Panko74/ESP32-Remote-CW-Keyer/schema/ESP32Keyer.kicad_sch

## KiCad design schema/ESP32Keyer.kicad_sch (2026-07-10)

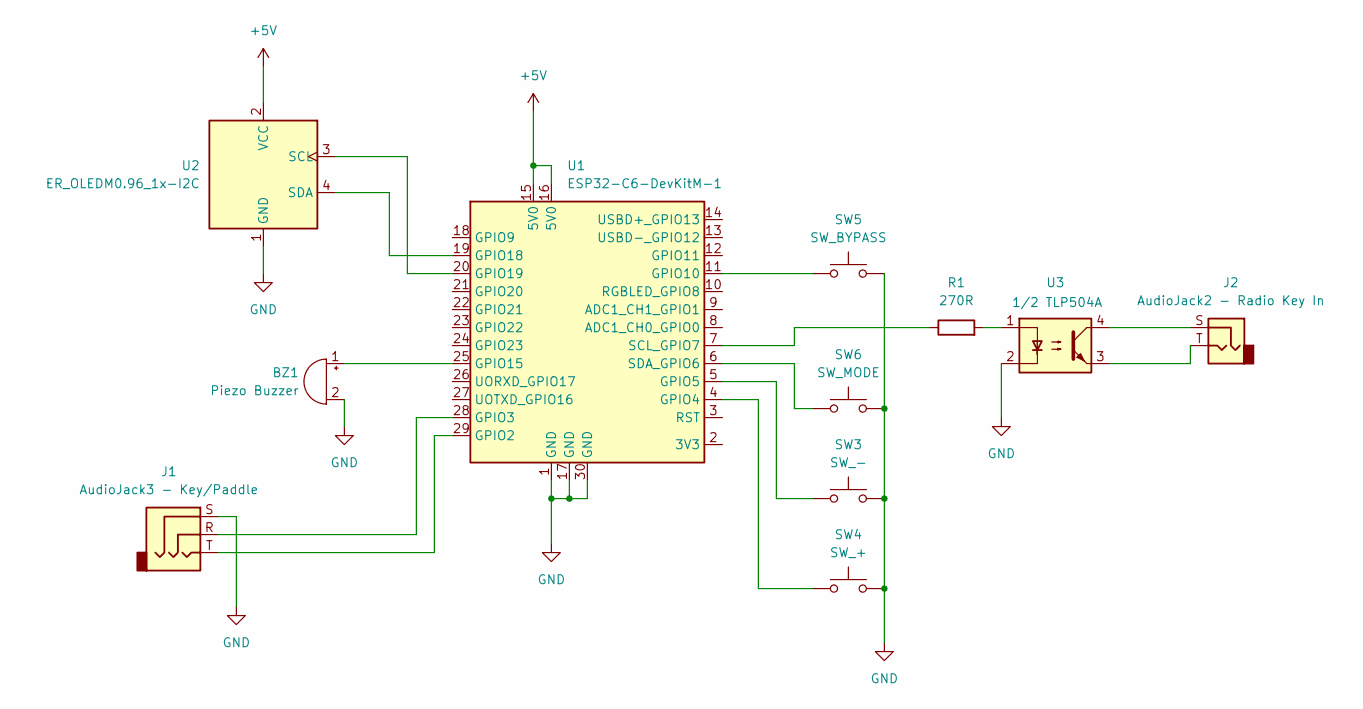
[picture p10: schematic ESP32Keyer.kicad_sch]

Parts:
BZ1: Piezo Buzzer
J1: AudioJack3 - Key/Paddle
J2: AudioJack2 - Radio Key In
R1: 270R
SW3: SW_-
SW4: SW_+
SW5: SW_BYPASS
SW6: SW_MODE
U1: ESP32-C6-DevKitM-1; ESP32-C3-DevKitM-1
U2: ER_OLEDM0.96_1x-I2C; ER_OLEDM0.91_1x-I2C
U3: 1/2 TLP504A

Connections:
+5V: U1.15 (5V0), U1.16 (5V0), U2.2 (VCC)
GND: BZ1.2 (-), J1.S, SW3.2, SW4.2, SW5.2, SW6.2, U1.1 (GND), U1.17 (GND), U1.30 (GND), U2.1 (GND), U3.2
unnamed: BZ1.1 (+), U1.25 (GPIO15)
unnamed: J1.R, U1.28 (GPIO3)
unnamed: J1.T, U1.29 (GPIO2)
unnamed: J2.S, U3.4
unnamed: J2.T, U3.3
unnamed: R1.1, U1.7 (SCL_GPIO7)
unnamed: R1.2, U3.1
unnamed: SW3.1, U1.5 (GPIO5)
unnamed: SW4.1, U1.4 (GPIO4)
unnamed: SW5.1, U1.11 (GPIO10)
unnamed: SW6.1, U1.6 (SDA_GPIO6)
unnamed: U1.19 (GPIO18), U2.4 (SDA)
unnamed: U1.20 (GPIO19), U2.3 (SCL)
